Yuno-20EA/MiniSumorobot/Mechanical/Anh_Chup_CacMatLinhKien/Mat_Ben2 (1).png

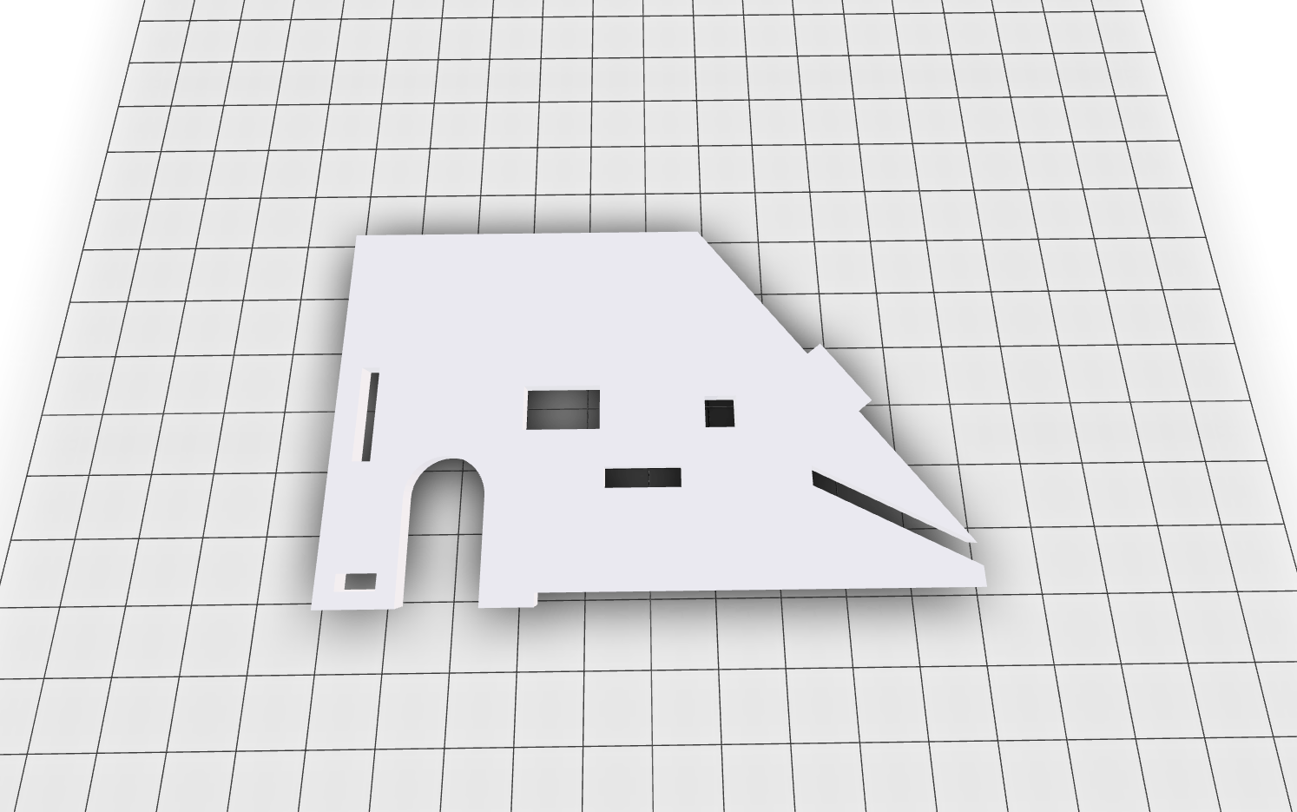
Mechanical/Anh_Chup_CacMatLinhKien/Mat_Ben2 (1).png
