Yuno-20EA/MiniSumorobot/Mechanical/Anh_Chup_CacMatLinhKien/Mat_Chua_Dong_Co.png

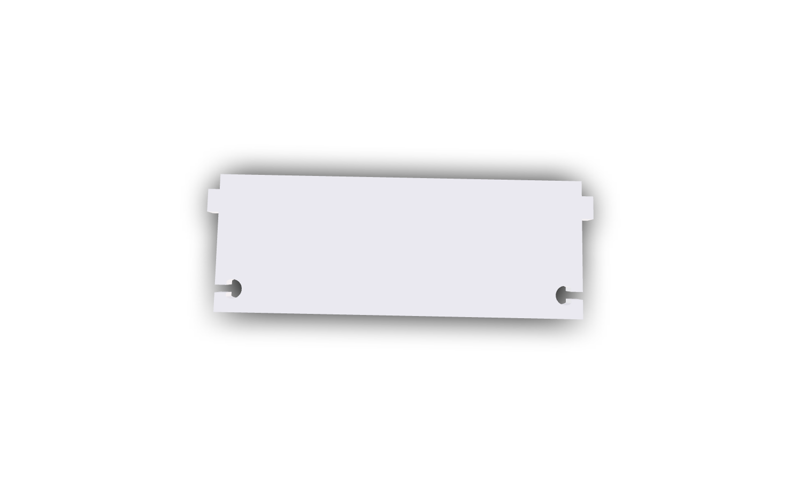
Mechanical/Anh_Chup_CacMatLinhKien/Mat_Chua_Dong_Co.png
