Yuno-20EA/MiniSumorobot/Mechanical/Anh_Chup_CacMatLinhKien/Mat_Chua_ViDieuKhien.png

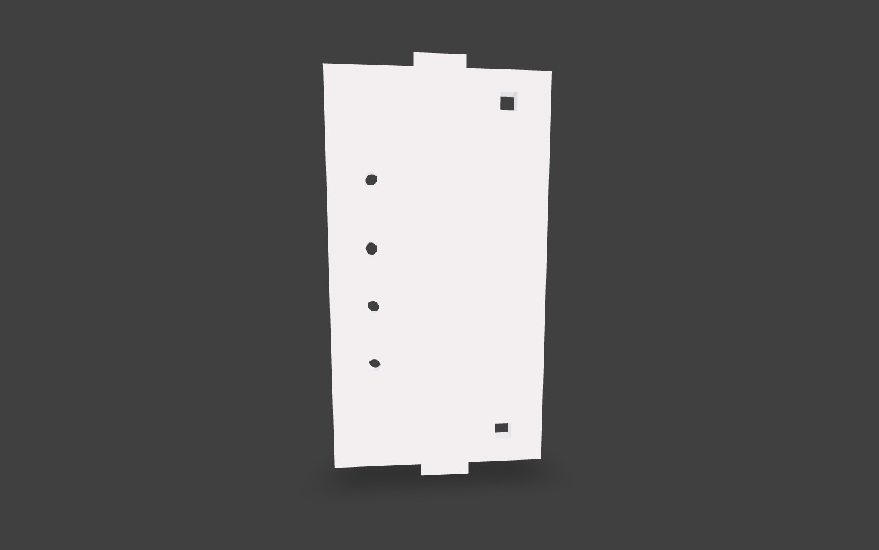
Mechanical/Anh_Chup_CacMatLinhKien/Mat_Chua_ViDieuKhien.png
