Yuno-20EA/MiniSumorobot/Mechanical/Anh_Chup_CacMatLinhKien/Mat_Phang_Luoi (1).png

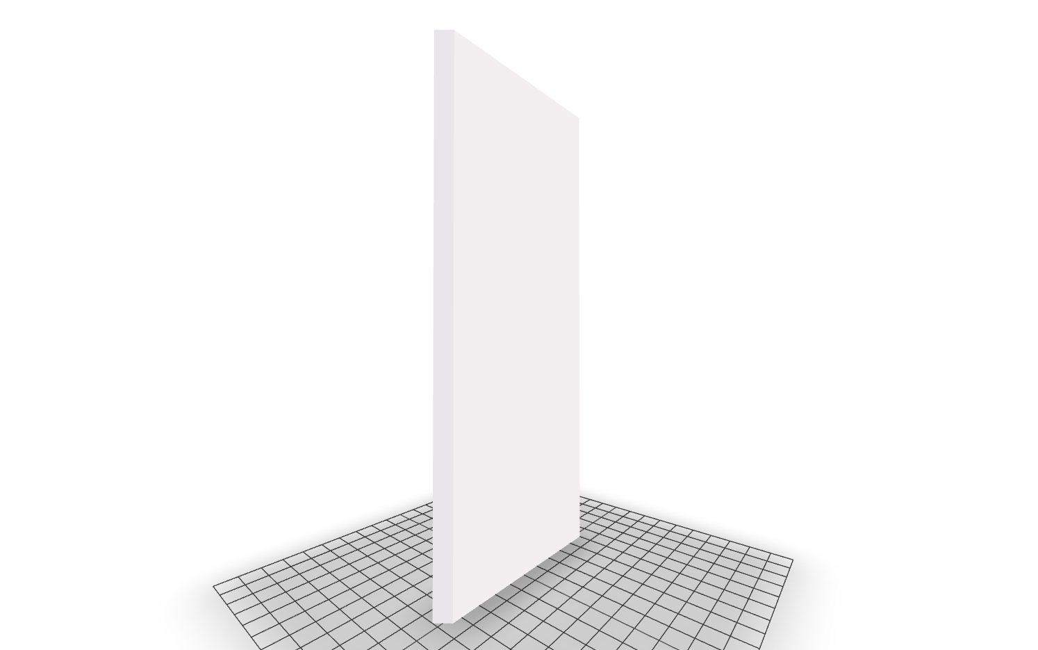
Mechanical/Anh_Chup_CacMatLinhKien/Mat_Phang_Luoi (1).png
