Yuno-20EA/MiniSumorobot/Mechanical/Anh_Chup_CacMatLinhKien/Mat_Phang_Luoi.png

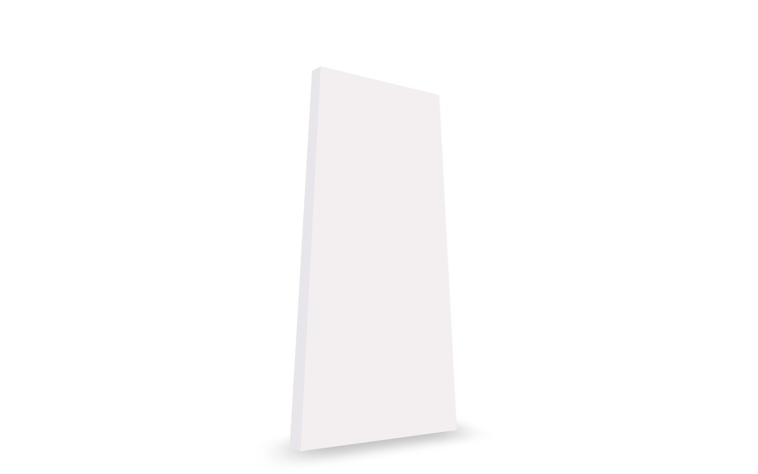
Mechanical/Anh_Chup_CacMatLinhKien/Mat_Phang_Luoi.png
